miclle/vinyl-record-player/previews/dimensions.png

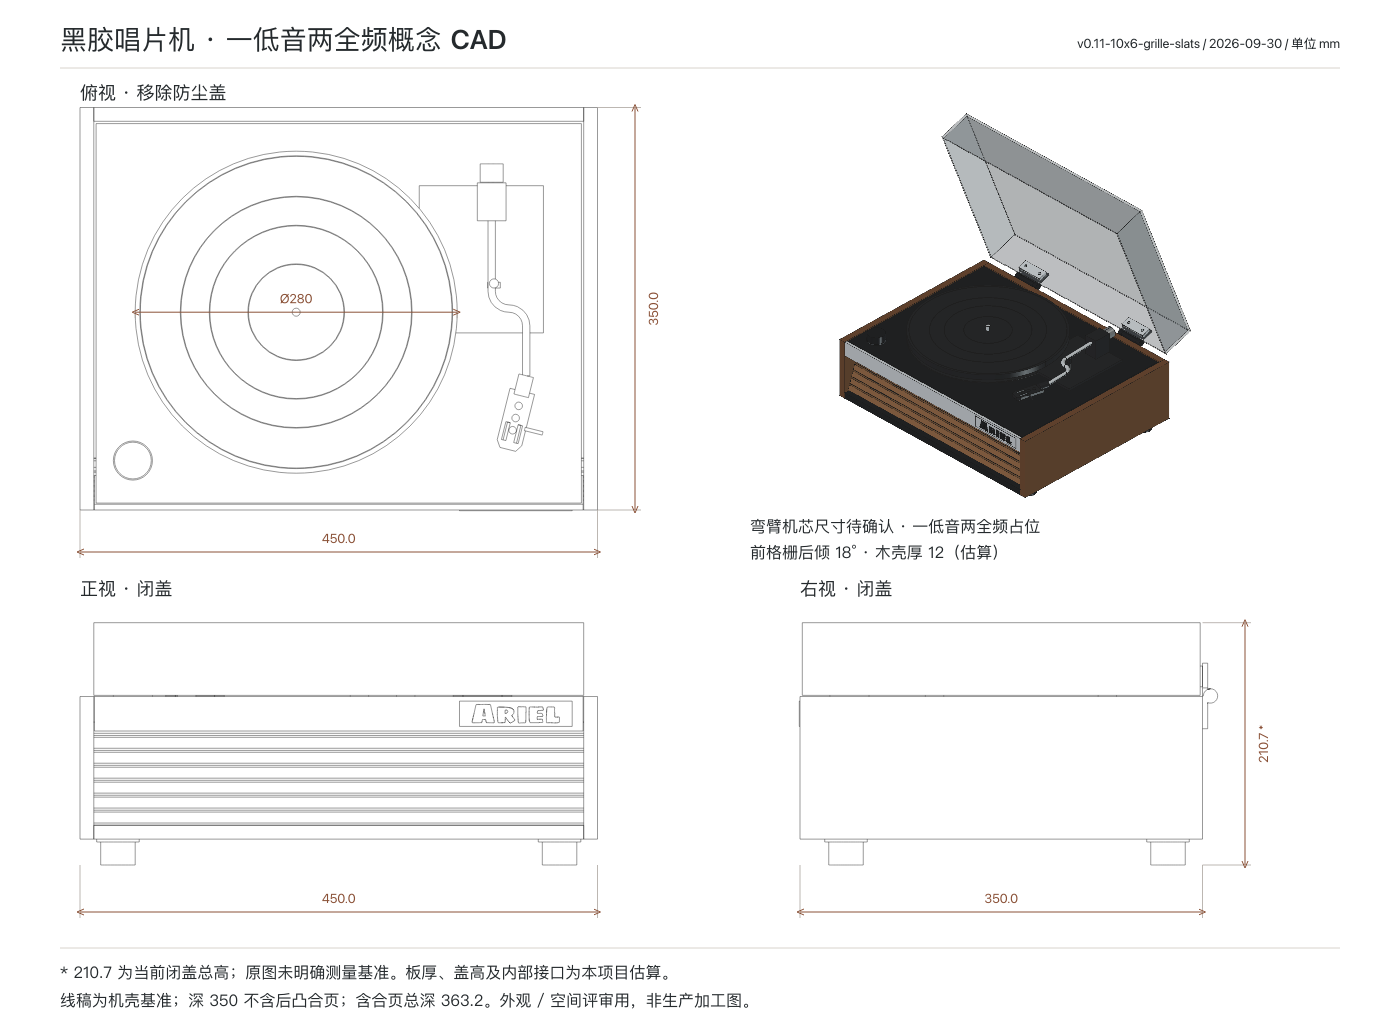
previews/dimensions.png
