miclle/vinyl-record-player/previews/front.png

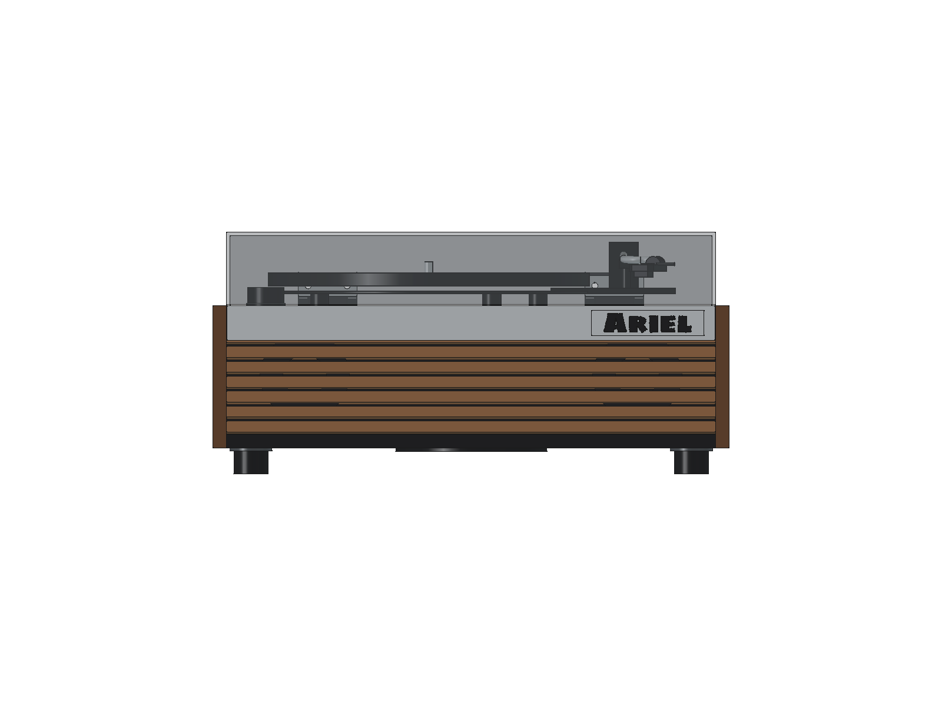
previews/front.png
