miclle/vinyl-record-player/previews/nameplate-artwork.png

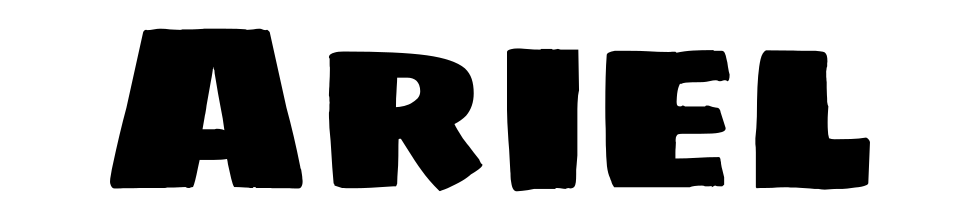
previews/nameplate-artwork.png
