miclle/vinyl-record-player/previews/right.png

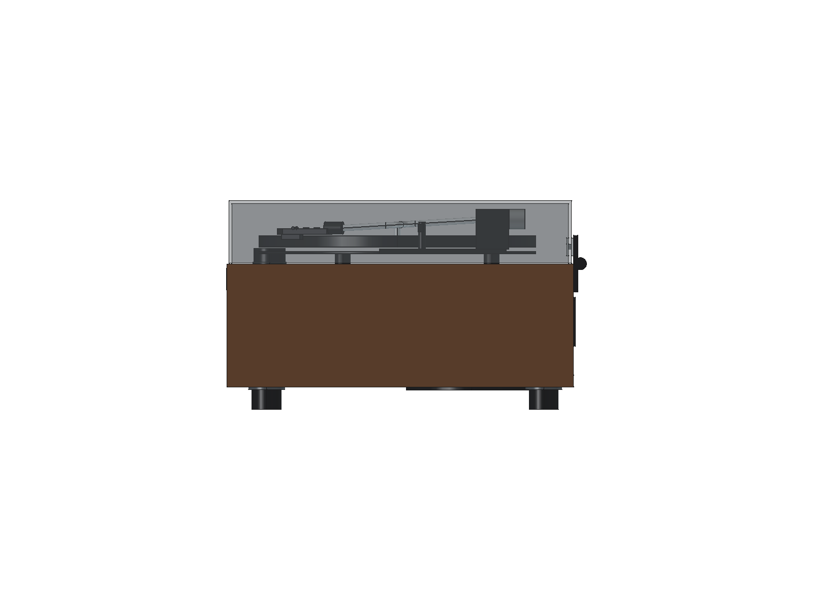
previews/right.png
