miclle/vinyl-record-player/previews/top.png

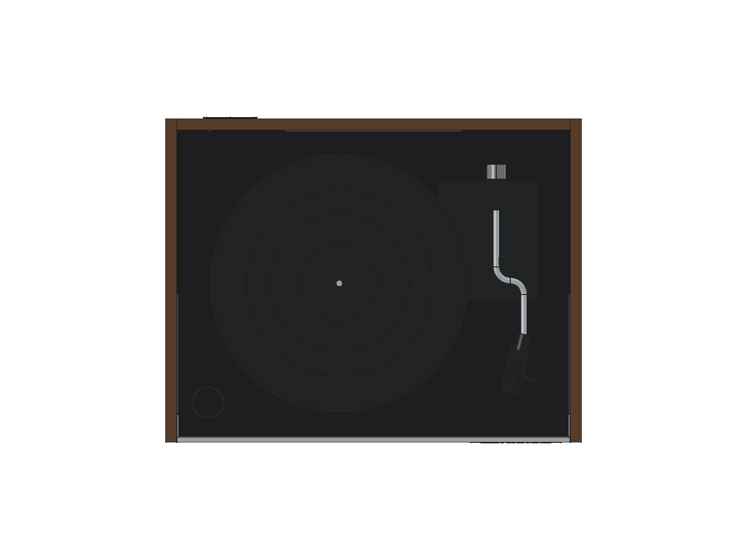
previews/top.png
