miclle/vinyl-record-player/references/ac-inlet/vendor-product.png

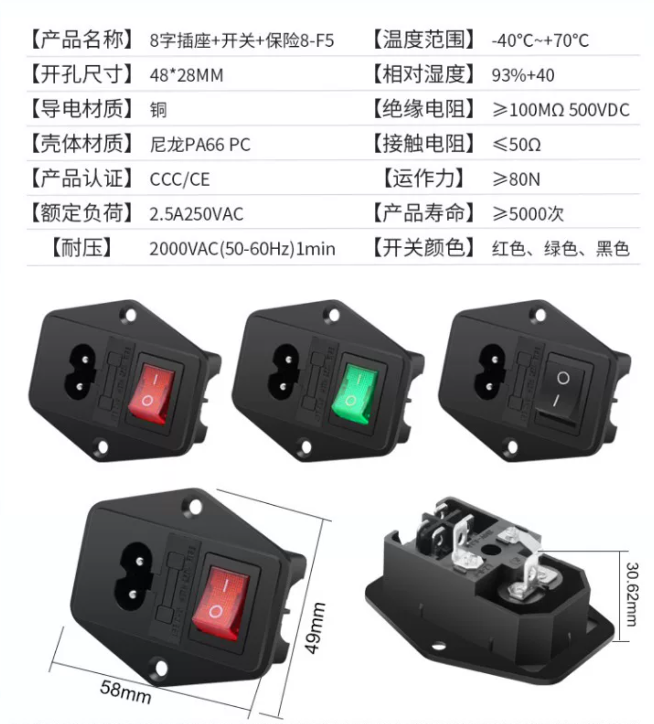
references/ac-inlet/vendor-product.png
