miclle/vinyl-record-player/references/fascia/vendor-dimensions.png

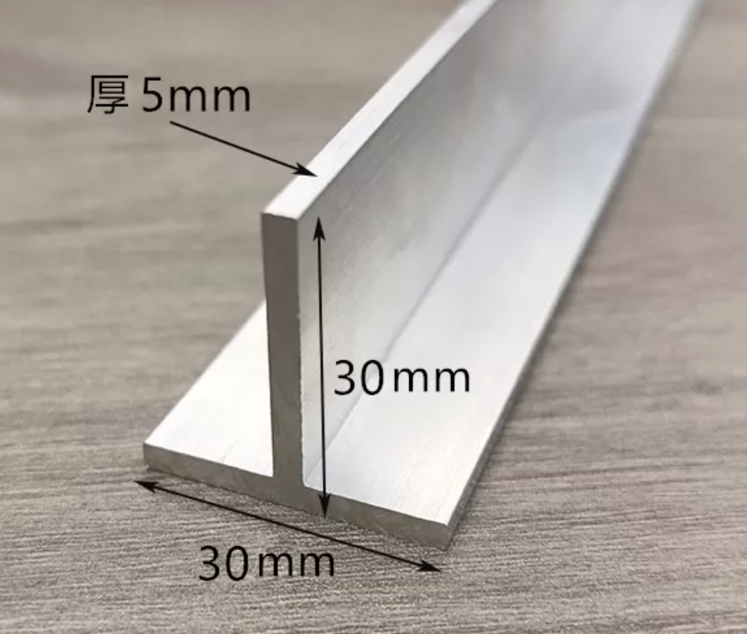
references/fascia/vendor-dimensions.png
