miclle/vinyl-record-player/references/feet/vendor-foot-dimensions.png

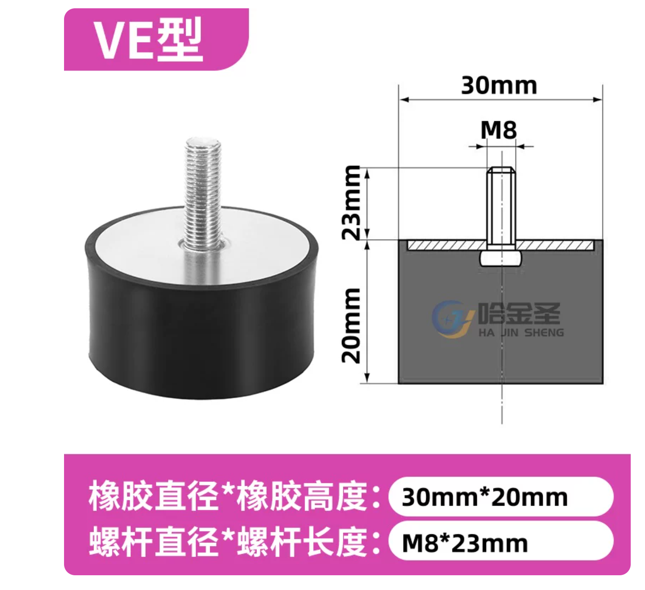
references/feet/vendor-foot-dimensions.png
