miclle/vinyl-record-player/references/feet/vendor-mount-dimensions.png

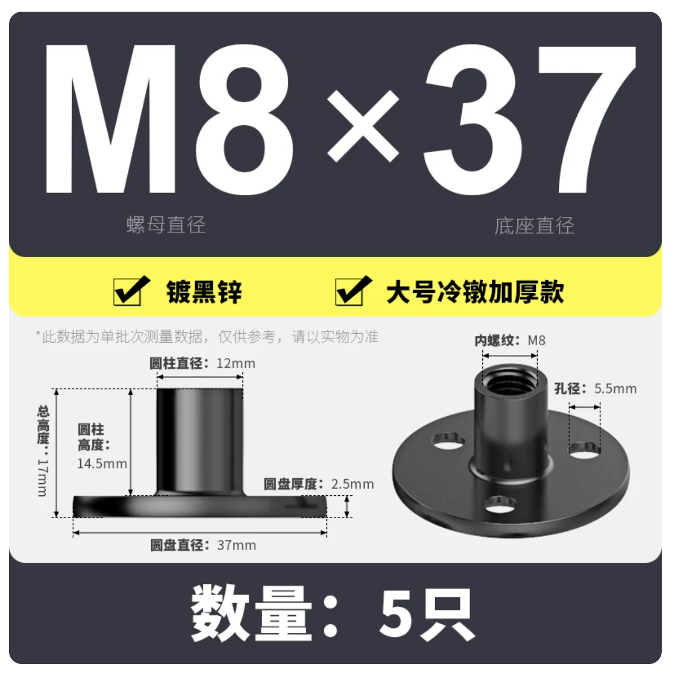
references/feet/vendor-mount-dimensions.png
