miclle/vinyl-record-player/references/hym-lumi/angle.jpg

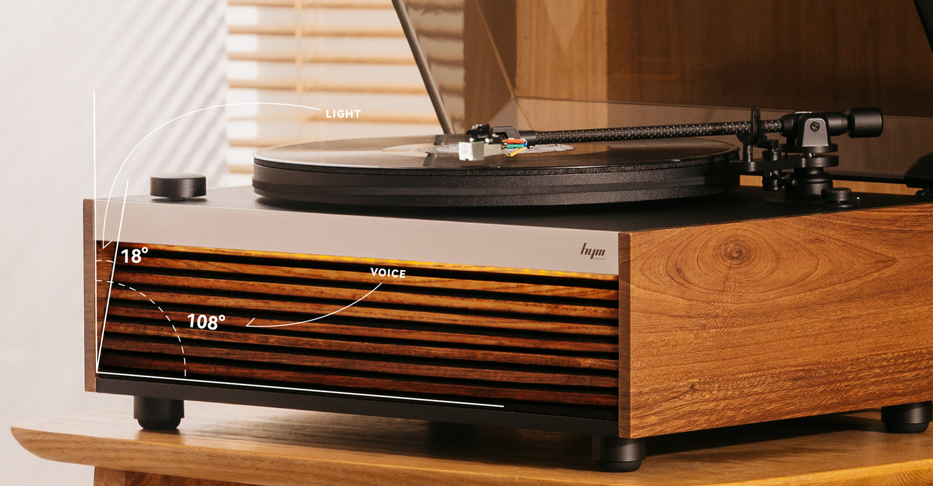
references/hym-lumi/angle.jpg
