miclle/vinyl-record-player/references/hym-lumi/closed.jpg

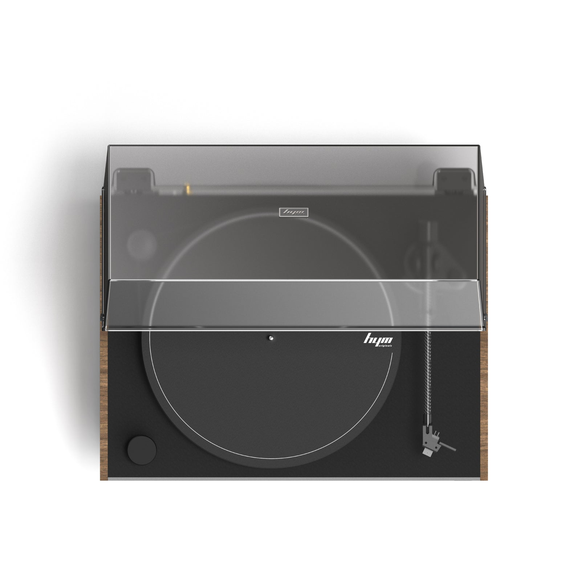
references/hym-lumi/closed.jpg
