miclle/vinyl-record-player/references/hym-lumi/front.jpg

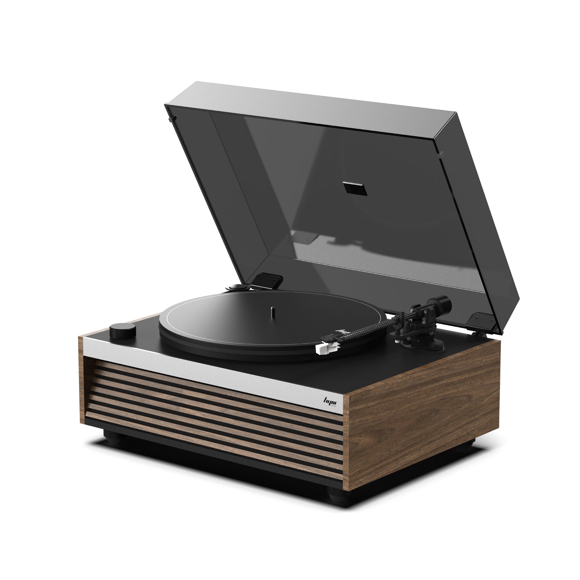
references/hym-lumi/front.jpg
