miclle/vinyl-record-player/references/mechanism/curved-arm-kit.png

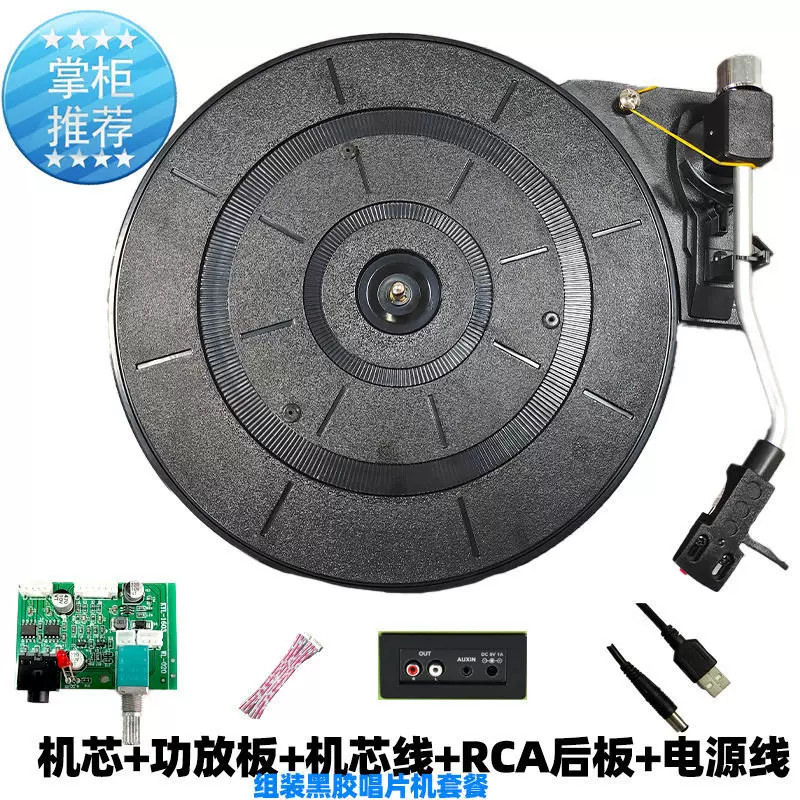
references/mechanism/curved-arm-kit.png
