miclle/vinyl-record-player/references/mechanism/straight-arm-dimensions.png

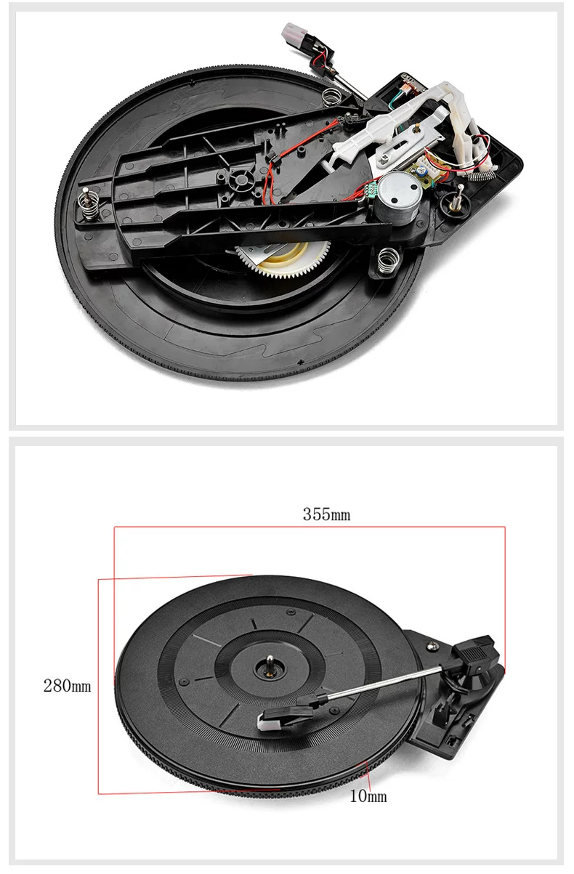
references/mechanism/straight-arm-dimensions.png
