miclle/vinyl-record-player/previews/assembly-guide-1.png

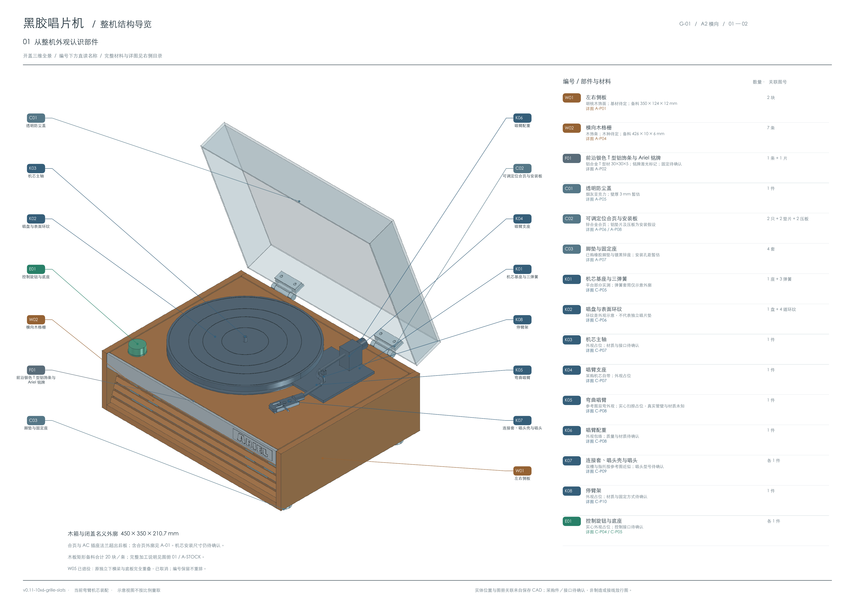
previews/assembly-guide-1.png
