miclle/vinyl-record-player/previews/assembly-guide-2.png

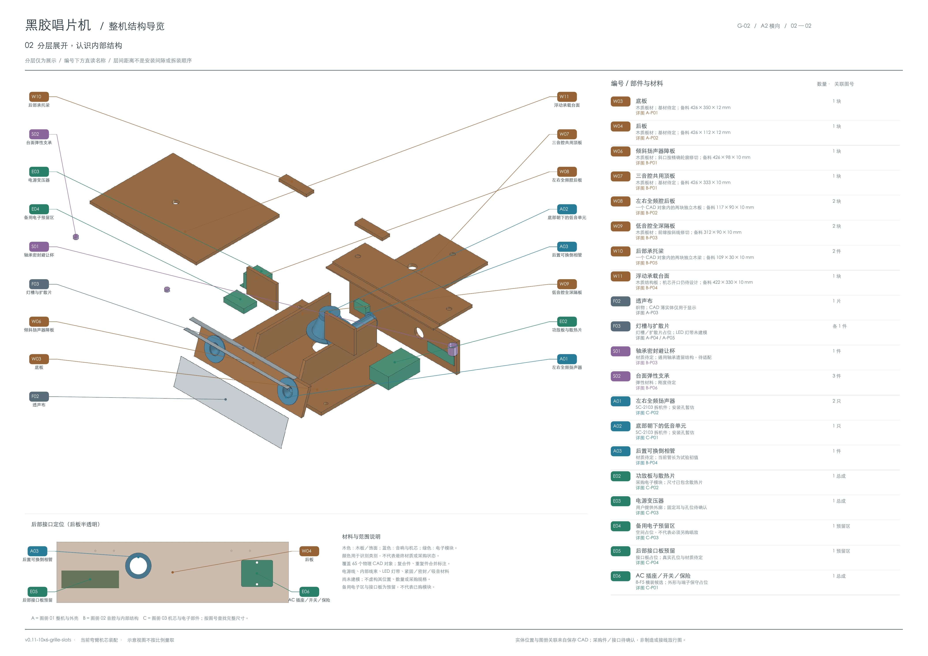
previews/assembly-guide-2.png
